Imogen-Wren-Studios/esp32-faerfly/image-sources/8-bit-heart-2.png

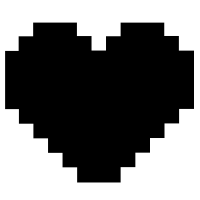
image-sources/8-bit-heart-2.png
