Imogen-Wren-Studios/esp32-faerfly/image-sources/cute-kitten-domestic-pet-pixel.png

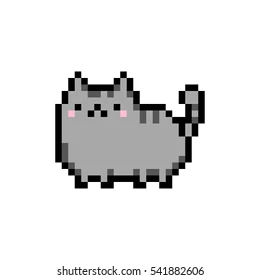
image-sources/cute-kitten-domestic-pet-pixel.png
