Imogen-Wren-Studios/esp32-faerfly/firmware/freeRTOS-stateMachine/globals.h

/*
 *  Globals
 * 
 * 
 */


#ifndef globals_h
#define globals_h

// User Options



void fastled_setup(){

//Serial.begin(115200);
  
 // Serial.println("Gathering Spectrum...");
  delay( 1000 ); // power-up safety delay
  FastLED.addLeds<LED_TYPE, LED_PIN, COLOR_ORDER>(leds, NUM_LEDS).setCorrection( TypicalLEDStrip );
 // Serial.println("...Processing Light Threads...");
  FastLED.setBrightness(  BRIGHTNESS );

  randomSeed(analogRead(0));   // psudo random number generator for randomness & chaos

  leds(0, NUM_LEDS) = CHSV(230, 50, 100);

 // Serial.println("               Weaving Colours...  \n     ...Selecting Pigments\n");
  delay(500);
//  Serial.println("Chroma Paintbrush Initialised:  Luminescence Matrix Applied.\n Starting Visual Light Imbument\n ");
  FastLED.show();  
}



CRGBPalette16 currentPalette;
TBlendType    currentBlending;


CRGBPalette16 nextPalette;
//TBlendType    currentBlending;



void fastLEDcontroller(){


  
}









 #endif
