Imogen-Wren-Studios/esp32-faerfly/firmware/unicornObject_verybasictest/unicornObject_verybasictest.ino

#include "unicornObject.h"



#include "pridePalettes.h"

#define START_PALETTE RainbowColors_p  // Sterile while palette to start with
#define SECOND_PALETTE trans






unicornObject unicorn;



void setup() {
  Serial.begin(115200);

  unicorn.begin();
  unicorn.currentPalette = START_PALETTE;
  // unicorn.nextPalette = SECOND_PALETTE;
  unicorn.paintRGB(255, 255, 0);

  delay(500);
}




void loop() {
  //unicorn.paintRGB(250, 250, 250);
 // 

  unicorn.fillBufferSmooth(START_PALETTE, 1000);

  // unicorn.fillBufferPaletteColors(START_PALETTE);


  unicorn.update();
}
